jetperch/js220_end_panels/eagle/fp_binding_posts/js220_fp_binding_posts_bom.tsv

Quantity | Part | Designators
2 | 111-0702-001 | J2,J3
1 | 111-0703-001 | J1
1 | 111-0707-001 | J4
1 | TSM-103-01-S-DV-A | J5
1 | JS220_fp_binding_post_pcb_revC | PCB1
