jetperch/js220_end_panels/eagle/fp_binding_posts/js220_fp_binding_posts_bom.xlsx

Sheet: All
BOM - All
2022 June 16
# | Qty | Ref Des | Name
1 | 2 | J2, J3 | 111-0702-001
2 | 1 | J1 | 111-0703-001
3 | 1 | J4 | 111-0707-001
4 | 1 | J5 | TSM-103-01-S-DV-A
5 | 1 | PCB1 | JS220_fp_binding_post_pcb_revC
 | 6

Sheet: Top
BOM - Top
2022 June 16
# | Qty | Ref Des | Name
1 | 2 | J2, J3 | 111-0702-001
2 | 1 | J1 | 111-0703-001
3 | 1 | J4 | 111-0707-001
4 | 1 | J5 | TSM-103-01-S-DV-A
5 | 1 | PCB1 | JS220_fp_binding_post_pcb_revC
 | 6

Sheet: Bottom
BOM - Bottom
2022 June 16
# | Qty | Ref Des | Name
 | 0
