jetperch/js220_end_panels/eagle/fp_binding_posts/js220_fp_binding_posts_build_report.xlsx

Sheet: 1
1 - js220_fp_binding_posts_revB - 1
status | name | qty_required | qty_stock | qty_arriving | qty_total | qty_short | arriving
stocked | 111-0707-001 | 1 | 3054 | 0 | 3054 | 0 | 2021-08-05
stocked | TSM-103-01-S-DV-A | 1 | 5 | 2000 | 2005 | 0 | 1970-01-01
stocked | JS220_fp_bp_pcb_revB | 1 | 20 | 0 | 20 | 0 | 1970-01-01
stocked | 111-0703-001 | 1 | 1225 | 0 | 1225 | 0 | 1970-01-01
stocked | 111-0702-001 | 2 | 1225 | 1400 | 2625 | 0 | 1970-01-01

Sheet: 2
2 - js220_fp_binding_posts_revB - 30
status | name | qty_required | qty_stock | qty_arriving | qty_total | qty_short | arriving
short | JS220_fp_bp_pcb_revB | 30 | 19 | 0 | 19 | 11 | 401404
arriving | TSM-103-01-S-DV-A | 30 | 4 | 2000 | 2004 | 0 | 2022-04-01
stocked | 111-0703-001 | 30 | 1224 | 0 | 1224 | 0 | 2021-10-29
stocked | 111-0702-001 | 60 | 1223 | 1400 | 2623 | 0 | 2021-10-29
stocked | 111-0707-001 | 30 | 3053 | 0 | 3053 | 0 | 2021-08-05

Sheet: 3
3 - js220_fp_binding_posts_revB - 250
status | name | qty_required | qty_stock | qty_arriving | qty_total | qty_short | arriving
short | JS220_fp_bp_pcb_revB | 250 | 0 | 0 | 0 | 250 | 401404
arriving | TSM-103-01-S-DV-A | 250 | 0 | 1974 | 1974 | 0 | 2022-04-01
stocked | 111-0707-001 | 250 | 3023 | 0 | 3023 | 0 | 2021-10-29
stocked | 111-0703-001 | 250 | 1194 | 0 | 1194 | 0 | 2021-10-29
stocked | 111-0702-001 | 500 | 1163 | 1400 | 2563 | 0 | 2021-10-29

Sheet: 4
4 - js220_fp_binding_posts_revB - 500
status | name | qty_required | qty_stock | qty_arriving | qty_total | qty_short | arriving
short | JS220_fp_bp_pcb_revB | 500 | 0 | 0 | 0 | 500 | 401404
arriving | TSM-103-01-S-DV-A | 500 | 0 | 1724 | 1724 | 0 | 2022-04-01
arriving | 111-0702-001 | 1000 | 663 | 1400 | 2063 | 0 | 2022-03-09
stocked | 111-0707-001 | 500 | 2773 | 0 | 2773 | 0 | 2021-10-29
stocked | 111-0703-001 | 500 | 944 | 0 | 944 | 0 | 2021-10-29

Sheet: 5
5 - js220_fp_binding_posts_revB - 500
status | name | qty_required | qty_stock | qty_arriving | qty_total | qty_short | arriving
short | JS220_fp_bp_pcb_revB | 500 | 0 | 0 | 0 | 500 | 401404
short | 111-0703-001 | 500 | 444 | 0 | 444 | 56 | 401404
arriving | TSM-103-01-S-DV-A | 500 | 0 | 1224 | 1224 | 0 | 2022-04-01
arriving | 111-0702-001 | 1000 | 0 | 1063 | 1063 | 0 | 2022-03-09
stocked | 111-0707-001 | 500 | 2273 | 0 | 2273 | 0 | 2021-10-29
